charles-waite/Retropie-Switch/resources/Prototype-Partially-Assembled.jpeg

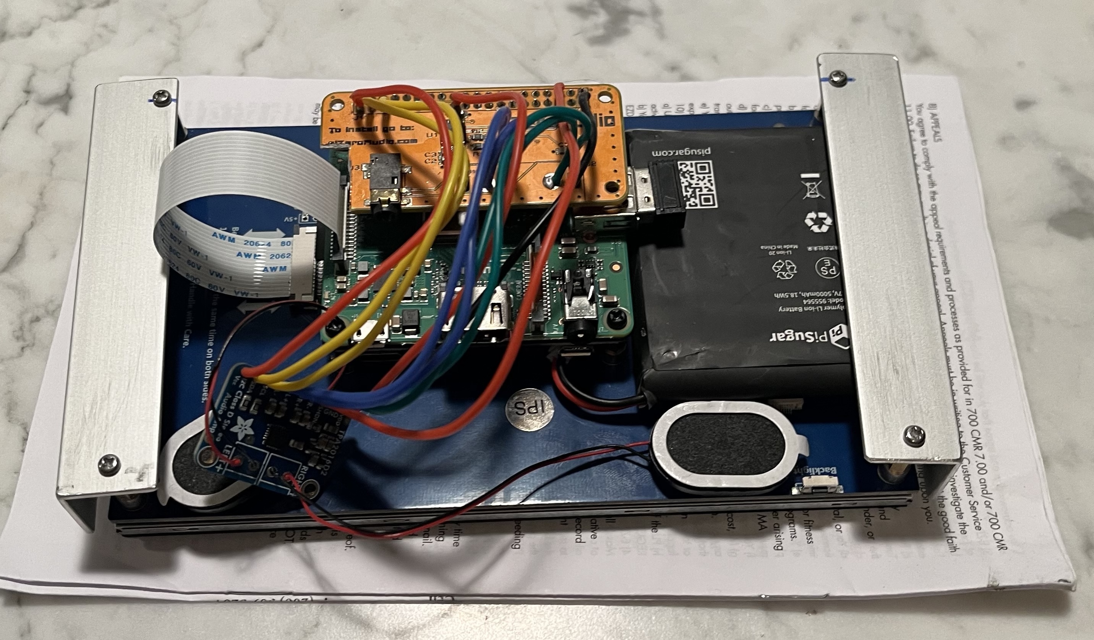
resources/Prototype-Partially-Assembled.jpeg
